impatrq/2025_722B_g2/hardware/power_electronics/Driver/Driver.kicad_sch

## KiCad design hardware/power_electronics/Driver/Driver.kicad_sch (2025-06-18)

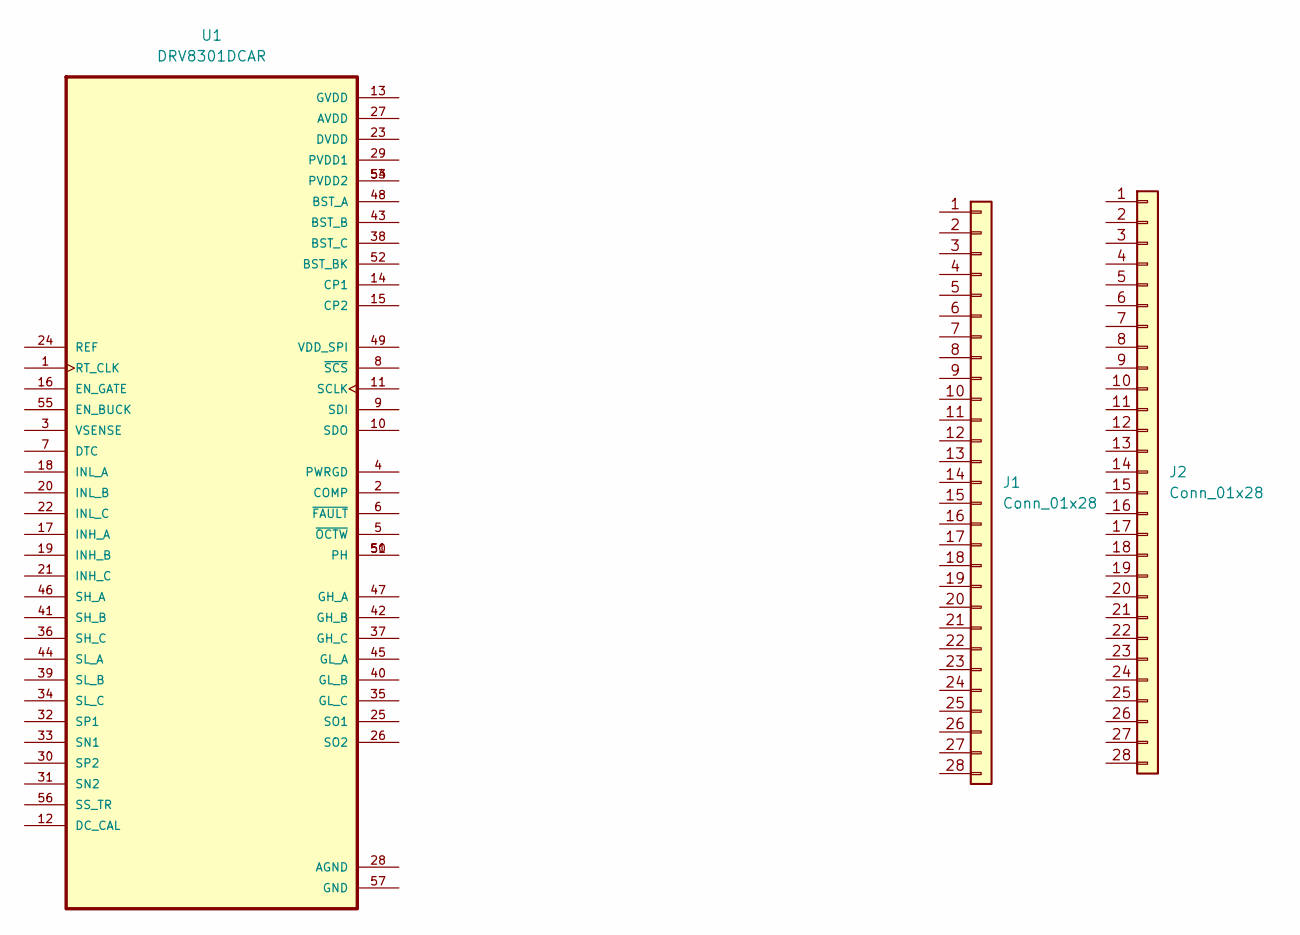
[picture p6: schematic Driver.kicad_sch]

Parts:
J1, J2: Conn_01x28
U1: DRV8301DCAR; SOP50P810X120-57N; PARTREV F

Connections:
unnamed: U1.50 (PH), U1.51 (PH)
unnamed: U1.53 (PVDD2), U1.54 (PVDD2)
