impatrq/2025_722B_g2/hardware/power_electronics/PCB/Aquiles PCB.kicad_sch

## KiCad design hardware/power_electronics/PCB/Aquiles PCB.kicad_sch (2025-07-15)

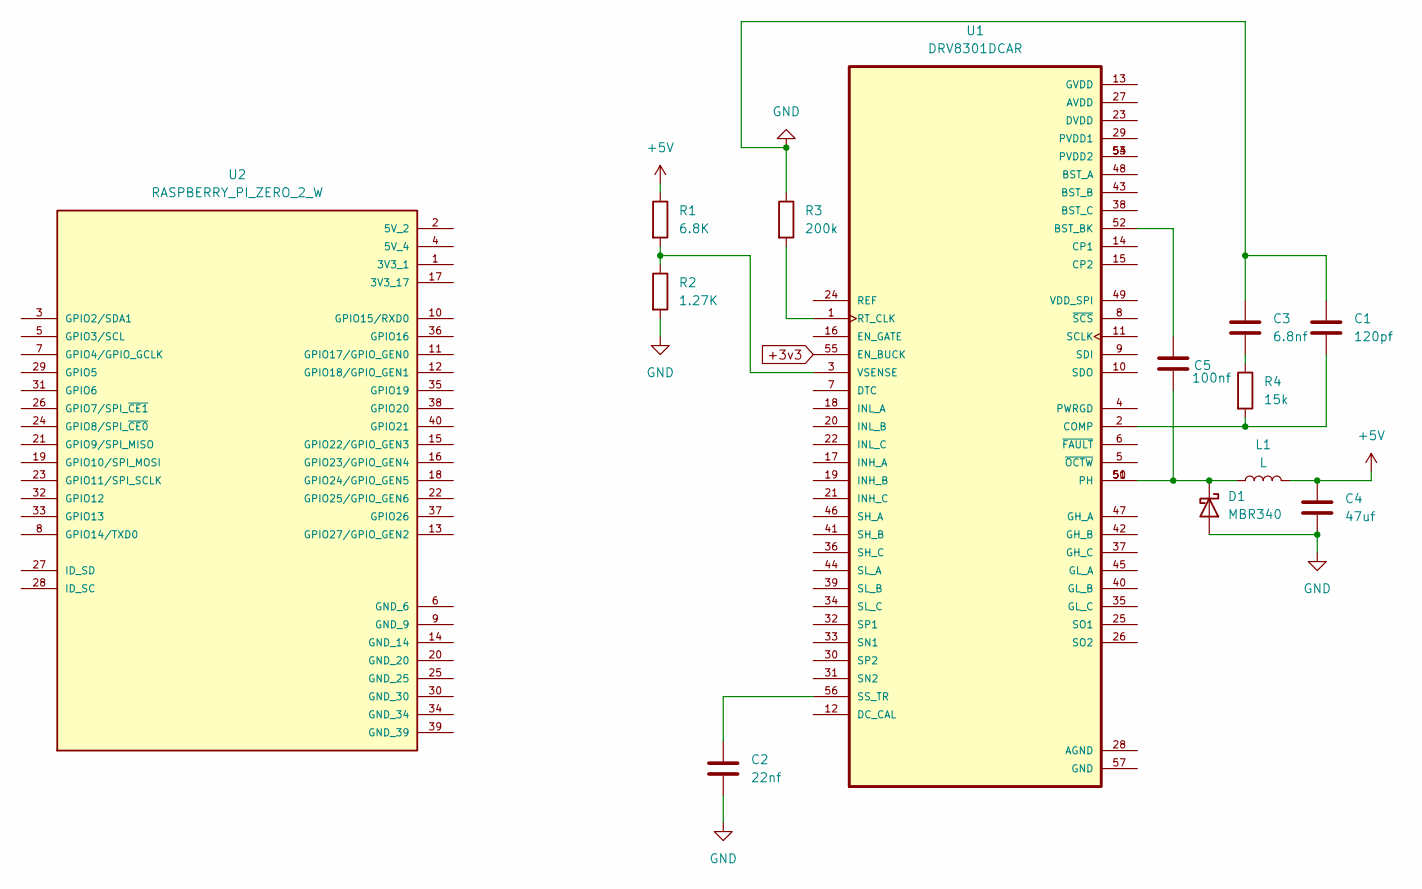
[picture p7: schematic Aquiles PCB.kicad_sch]

Parts:
C1: 120pf
C2: 22nf
C3: 6.8nf
C4: 47uf
C5: 100nf
D1: MBR340; D_DO-201AD_P15.24mm_Horizontal
L1: L
R1: 6.8K
R2: 1.27K
R3: 200k
R4: 15k
U1: DRV8301DCAR; SOP50P810X120-57N; PARTREV F
U2: RASPBERRY_PI_ZERO_2_W; MODULE_RASPBERRY_PI_ZERO_2_W; PARTREV April 2024

Connections:
+3v3: U1.55 (EN_BUCK)
+5V: C4.1, L1.2, R1.1
GND: C1.1, C2.2, C3.1, C4.2, D1.2 (A), R2.2, R3.1
unnamed: C1.2, R4.2, U1.2 (COMP)
unnamed: C2.1, U1.56 (SS_TR)
unnamed: C3.2, R4.1
unnamed: C5.1, U1.52 (BST_BK)
unnamed: C5.2, D1.1 (K), L1.1, U1.50 (PH), U1.51 (PH)
unnamed: R1.2, R2.1, U1.3 (VSENSE)
unnamed: R3.2, U1.1 (RT_CLK)
unnamed: U1.53 (PVDD2), U1.54 (PVDD2)
